IRNAS/gps-tag-lora-addon-hardware/release/gps-tag-lora-addon/v0_2/2-gps-tag-lora-addon-Board Assembly/Assembly Drawings.PDF

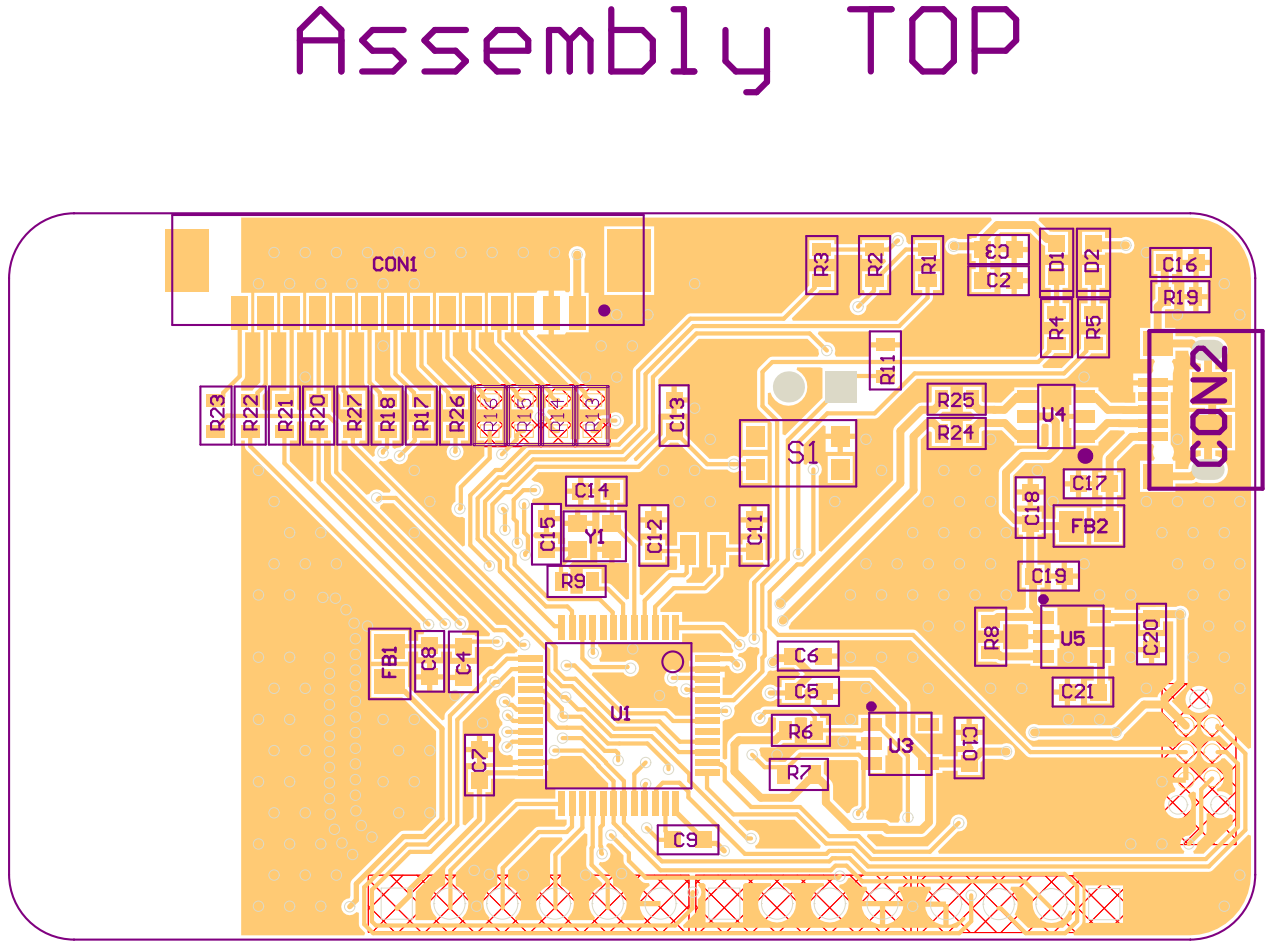
[picture p16: page 1]

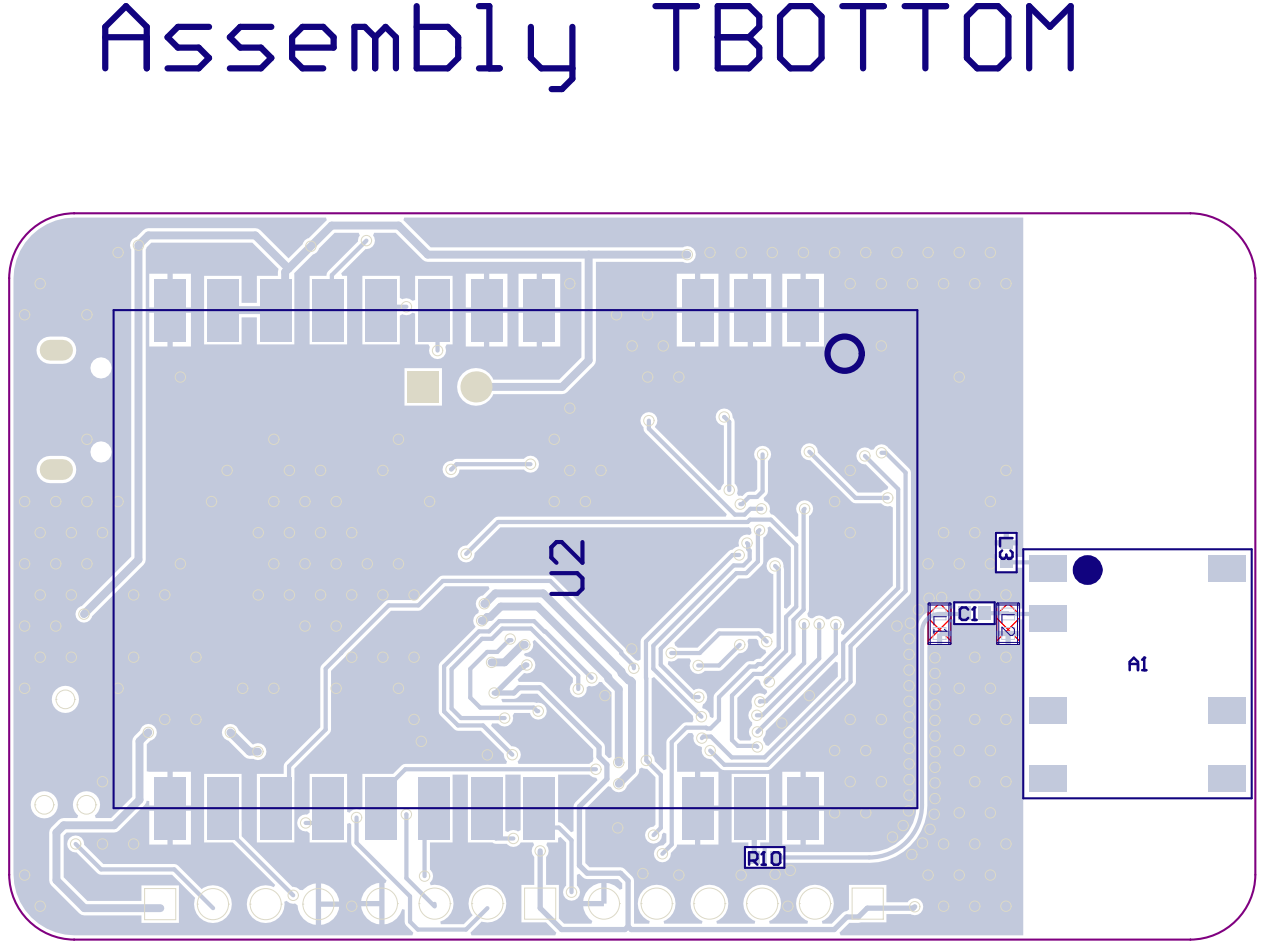
[picture p17: page 2]
